nirvaankohli/magnetic-chess-board/hardware/cad/3d-printed/pieces/king.stl

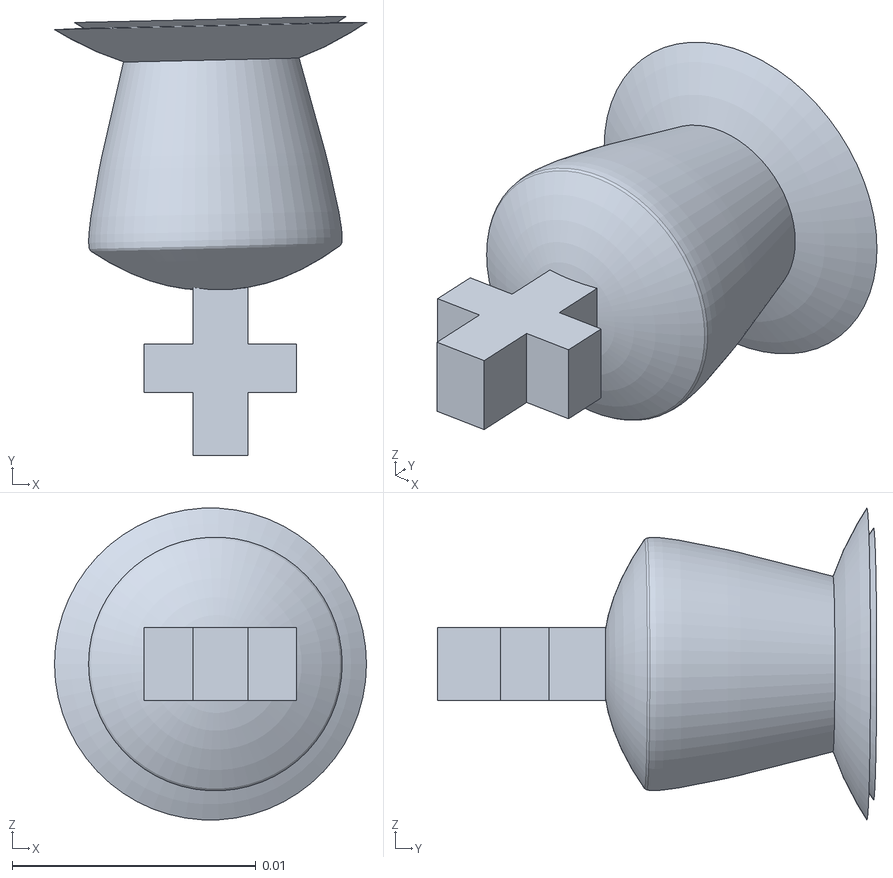
[picture p26: CAD file, 2026-06-13]
hardware/cad/3d-printed/pieces/king.stl
0.0128 x 0.018 x 0.0128
