nirvaankohli/magnetic-chess-board/hardware/cad/components/m3-5mm-screw.step

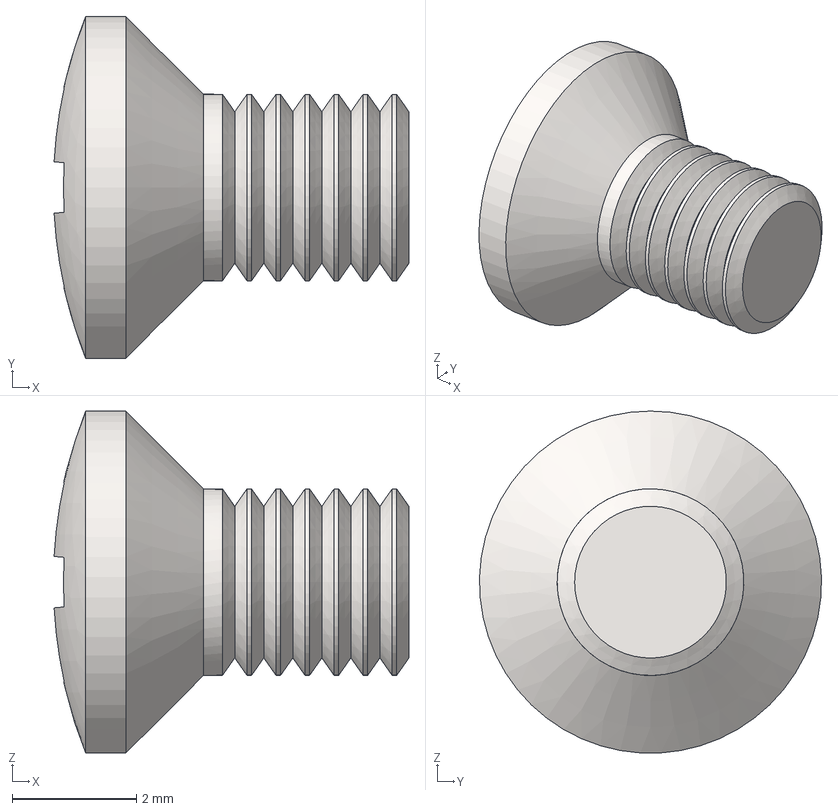
[picture p27: CAD file, 2026-06-13]
hardware/cad/components/m3-5mm-screw.step
5.70 x 5.50 x 5.50 mm
